Jozambra/DIY_BTSpeakerBox/Simulations/3BandEQsimulation.asc

C1: cap; 10µ
C2: cap; 33p
C3: cap; 2.2µ
C4: cap; 10µ
C5: cap; 10n
C6: cap; 10µ
C7: cap; 22n
C8: cap; 4.7n
C9: cap; 47n
R1: res; 44k
R2: res; 50k
R3: res; 50k
R4: res; 10k
R5: res; 10k
R6: res; 44k
R7: res; 10k
R8: res; 0
R9: res; 100k
R10: res; 10k
R11: res; 3.3k
R12: res; 25k
R13: res; 75k
R14: res; 3.6k
R15: res; 50k
R16: res; 50k
R17: res; 25k
R18: res; 10k
R19: res; 3.3k
R20: res; 3.6k
R21: res; 10k
R22: res; 50k
R23: res; 20k
U1: LT1006
U2: LT1006
U3: LT1006
V1: voltage; 9
V2: voltage; SINE(); AC 2.7 0
Named nets: 0, VCC, FB, Vbias
.ac dec 2000 2 200k
Amplification
Attenuation
